kuenrg153/bitLode/firmware/build.rs

use std::{env, fs::File, io::Write, path::PathBuf};

fn main() {
    let out = &PathBuf::from(env::var_os("OUT_DIR").unwrap());
    File::create(out.join("memory.x"))
        .unwrap()
        .write_all(include_bytes!("memory.x"))
        .unwrap();

    println!("cargo:rustc-link-search={}", out.display());
    println!("cargo:rerun-if-changed=memory.x");

    println!("cargo:rustc-link-arg-bins=--nmagic");
    println!("cargo:rustc-link-arg-bins=-Tlink.x");
    println!("cargo:rustc-link-arg-bins=-Tlink-rp.x");
    println!("cargo:rustc-link-arg-bins=-Tdefmt.x");
}
