kuenrg153/bitLode/firmware/src/control/i2c.rs

use embassy_embedded_hal::SetConfig;
use heapless::Vec;

use super::CommandError;

#[derive(defmt::Format)]
pub enum Command {
    SetFrequency { frequency: u32 },                         // 0x10
    Write { addr: u8, buf: Vec<u8, 256> },                   // 0x20
    Read { addr: u8, len: u8 },                              // 0x30
    WriteRead { addr: u8, buf: Vec<u8, 256>, read_len: u8 }, // 0x40
}

impl Command {
    pub fn from_bytes(buf: &[u8]) -> Result<Self, CommandError> {
        match buf {
            [0x10, b1, b2, b3, b4] => Ok(Self::SetFrequency {
                frequency: u32::from_le_bytes([*b1, *b2, *b3, *b4]),
            }),
            [0x20, addr, buf @ ..] => Ok(Self::Write {
                addr: *addr,
                buf: Vec::from_slice(buf).map_err(|_| CommandError::BufferOverflow)?,
            }),
            [0x30, addr, len] => Ok(Self::Read { addr: *addr, len: *len }),
            [0x40, addr, buf @ .., read_len] => Ok(Self::WriteRead {
                addr: *addr,
                buf: Vec::from_slice(buf).map_err(|_| CommandError::BufferOverflow)?,
                read_len: *read_len,
            }),
            _ => Err(CommandError::Invalid),
        }
    }
}

impl super::ControllerCommand for Command {
    async fn handle(&self, controller: &mut super::Controller) -> Result<Vec<u8, 256>, CommandError> {
        match self {
            Command::SetFrequency { frequency } => {
                let mut config = embassy_rp::i2c::Config::default();
                config.frequency = *frequency;
                controller.i2c.set_config(&config).map_err(|_| CommandError::Message("I2C Set Frequency Error"))?;
                Ok(Vec::from_slice(&frequency.to_le_bytes()).unwrap())
            }
            Command::Write { addr, buf } => {
                controller.i2c.write_async(*addr, buf.iter().copied()).await.map_err(|_| CommandError::Message("I2C Write Error"))?;
                Ok(Vec::from_slice(&[buf.len() as u8]).unwrap())
            }

            Command::Read { addr, len } => {
                let mut buf = Vec::new();
                let _ = buf.resize_default(*len as usize);
                controller.i2c.read_async(*addr, &mut buf).await.map_err(|_| CommandError::Message("I2C Read Error"))?;
                Ok(buf)
            }

            Command::WriteRead { addr, buf, read_len } => {
                let mut read_buf = Vec::new();
                let _ = read_buf.resize_default(*read_len as usize);
                controller
                    .i2c
                    .write_read_async(*addr, buf.iter().copied(), &mut read_buf[0..*read_len as usize])
                    .await
                    .map_err(|_| CommandError::Message("I2C WriteRead Error"))?;
                Ok(read_buf)
            }
        }
        //
    }
}
